SNO95/NIXIE_clock/20181021_120413.jpg

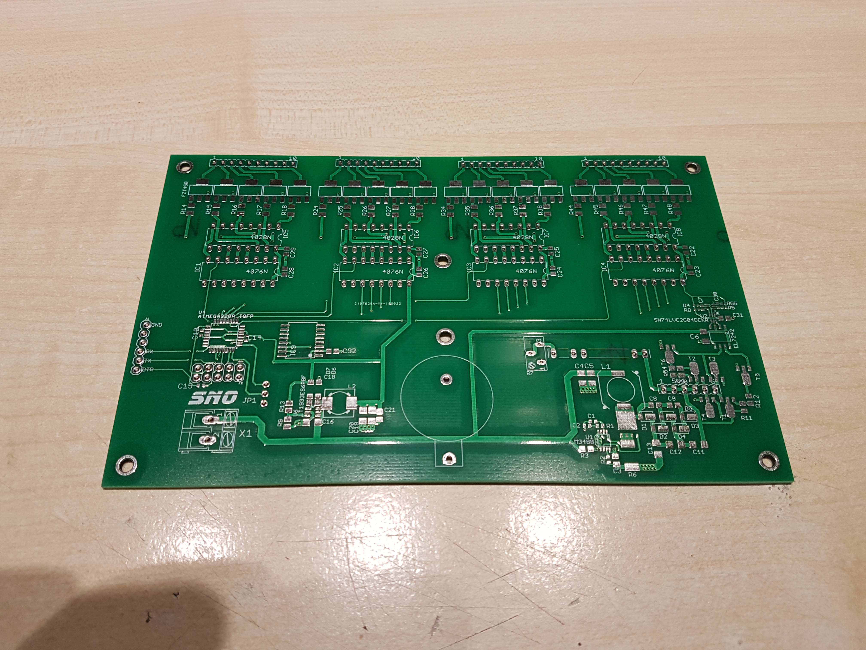
20181021_120413.jpg
